OreganoUser/CanSatProject/sensorsational_library/direction_control.h

#ifndef DIRECTION_CONTROL_H
#define DIRECTION_CONTROL_H

#include <Arduino.h>
#include <Servo.h>

#define TOLERANCE 5.0  // tolerance for the right angle

extern bool arms_deployed;

extern Servo servo_arms;
extern Servo escLeft;
extern Servo escRight;

void initMotors();
void adjustDirection();
void turnLeft(float delta);
void turnRight(float delta);
void moveForward();

#endif
